tody-agent/musedy/Computer/extracted_pics/982b4795acd97d9ea3addd309ae2284b.webp

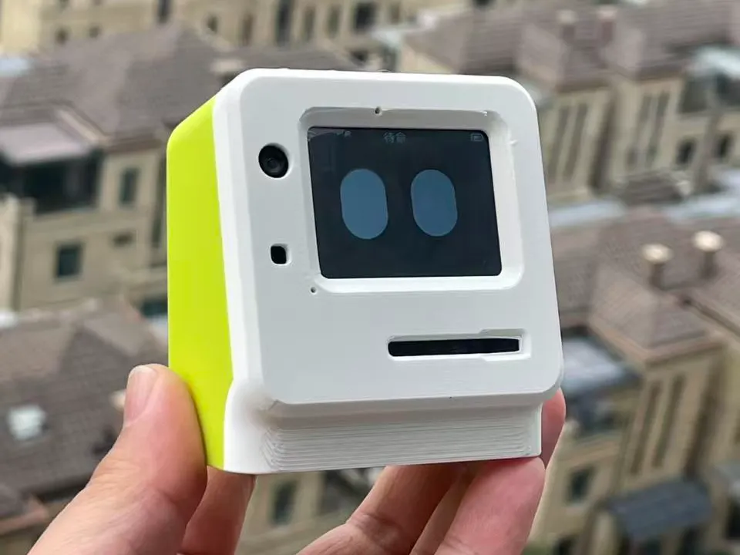
Computer/extracted_pics/982b4795acd97d9ea3addd309ae2284b.webp
