tody-agent/musedy/Computer/extracted_pics/f577b5d42854210b2fca52601f70b0d6.webp

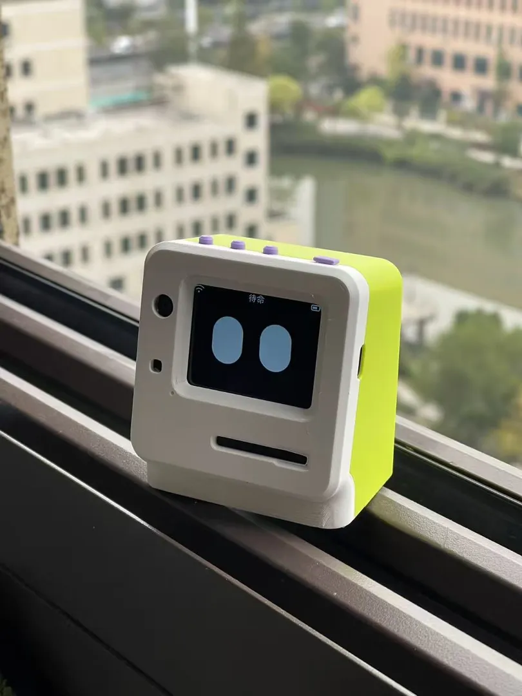
Computer/extracted_pics/f577b5d42854210b2fca52601f70b0d6.webp
