tody-agent/musedy/Computer/extracted_pics/pick_1.png

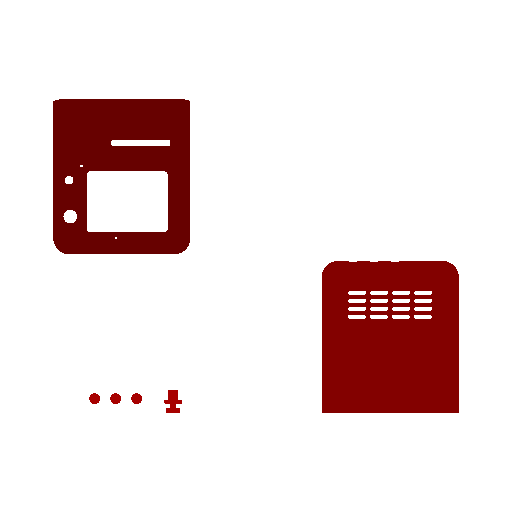
Computer/extracted_pics/pick_1.png
