tody-agent/musedy/Computer/extracted_pics/plate_1.png

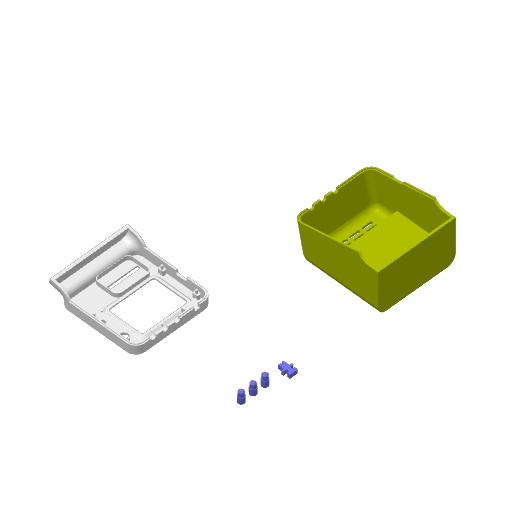
Computer/extracted_pics/plate_1.png
