tody-agent/musedy/Computer/extracted_pics/assembly_1.jpg

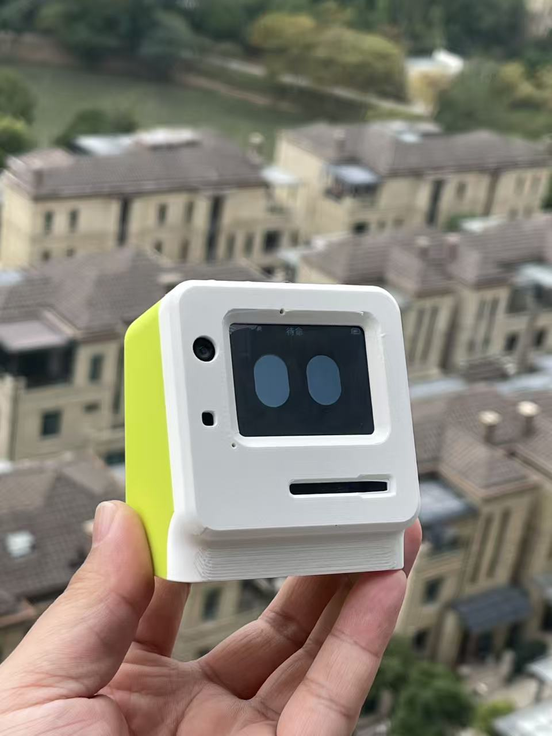
Computer/extracted_pics/assembly_1.jpg
