tody-agent/musedy/components/muse/esp_lcd_panel_st7735.h

/*
 * SPDX-FileCopyrightText: 2021-2024 Espressif Systems (Shanghai) CO LTD
 * SPDX-License-Identifier: Apache-2.0
 */

#pragma once

#include <stdbool.h>
#include "esp_err.h"
#include "esp_lcd_panel_io.h"
#include "esp_lcd_panel_dev.h"

#ifdef __cplusplus
extern "C" {
#endif

/**
 * @brief Create LCD panel for model ST7735 / ST7735S (1.8" 128x160 TFT LCD)
 *
 * Supports both portrait (128x160) and landscape (160x128) orientations with
 * configurable GRAM offsets (gap) and color inversion for IPS/TN panels.
 *
 * @param[in] io LCD panel IO handle
 * @param[in] panel_dev_config general panel device configuration
 * @param[out] ret_panel Returned LCD panel handle
 * @return
 *      - ESP_OK: Successfully initialized panel
 *      - ESP_ERR_INVALID_ARG: If parameter is invalid
 *      - ESP_ERR_NO_MEM: If memory allocation failed
 */
esp_err_t esp_lcd_new_panel_st7735(const esp_lcd_panel_io_handle_t io,
                                   const esp_lcd_panel_dev_config_t *panel_dev_config,
                                   esp_lcd_panel_handle_t *ret_panel);

#ifdef __cplusplus
}
#endif
